ytmytm/1551-RAMBOard/doc/1551-img_0627.jpg

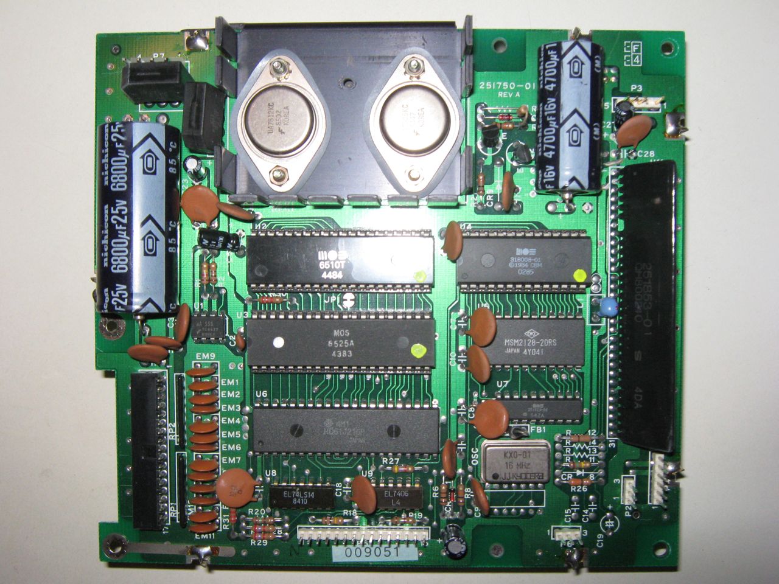
doc/1551-img_0627.jpg
