ytmytm/1551-RAMBOard/doc/nightrider-1551-2.jpg

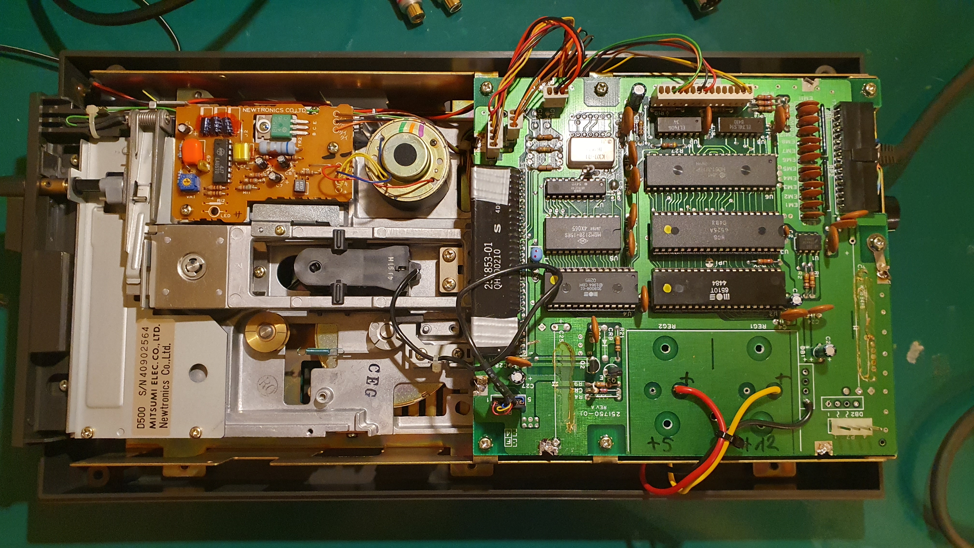
doc/nightrider-1551-2.jpg
